0felex01/MTT/SD_Reader.h

#include "KickSort.h"

#define MAX_FILES 100
#define MAX_FILENAME_LENGTH 100
#define TOP_BOUND_CURSOR_ROW 3

void draw_files(String files[MAX_FILES], int files_count, int cursor_pos, String locale) {
  u8g2.clearBuffer();
  int files_i = 0;

  if (files_count <= MAX_ROWS - 1 || cursor_pos < TOP_BOUND_CURSOR_ROW) {
    files_i = 0;
  } else if (cursor_pos >= TOP_BOUND_CURSOR_ROW) {
    files_i = cursor_pos - TOP_BOUND_CURSOR_ROW + 1;
  }

  for (int i = 0; i < MAX_ROWS - 1; ++i) {
    if (i < files_count) {
      OLED_print_line(files[files_i + i].c_str(), i, locale);
    }
  }
}

int get_files(String files[MAX_ROWS]) {
  File dir;
  File file;
  dir.open("/");
  int files_count = 0;
  char buf[MAX_FILENAME_LENGTH];
  while (file.openNext(&dir, O_READ) && files_count < 30) {
    file.getName(buf, sizeof(buf));
    if (buf[0] != '.' && buf[0] != '\0' && strcmp(buf, "System Volume Information")) { // Ignore hidden files and System Volume Information folder
      /* Serial.println(buf); */
      files[files_count] = String(buf);
      ++files_count;
    }
  }
  dir.close();
  file.close();

  // Sort files
  KickSort<String>::insertionSort(files, files_count);

  // Strip .srt extensions
  for (int i = 0; i < files_count; ++i) {
    int len = files[i].length();
    if (files[i].substring(len - 4, len) == ".srt") {
      files[i] = files[i].substring(0, len - 4);
    }
  }

  return files_count;
}
